dr-occams-r/AntivibrationFanMount/images/Fan4010-ModelView2.png

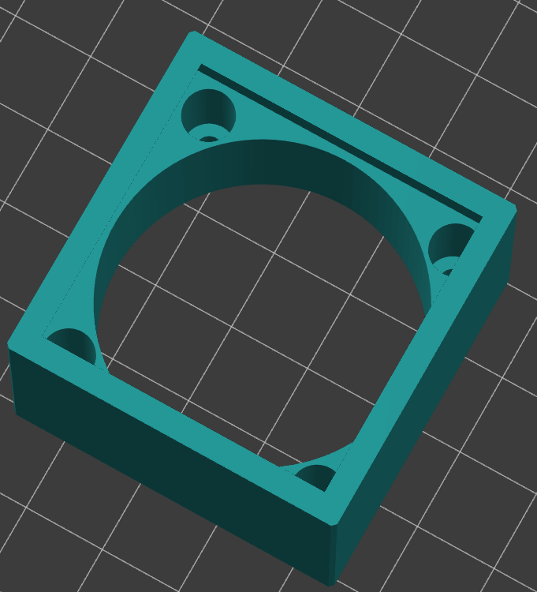
images/Fan4010-ModelView2.png
