dr-occams-r/AntivibrationFanMount/images/IMG_20240214_092702.jpg

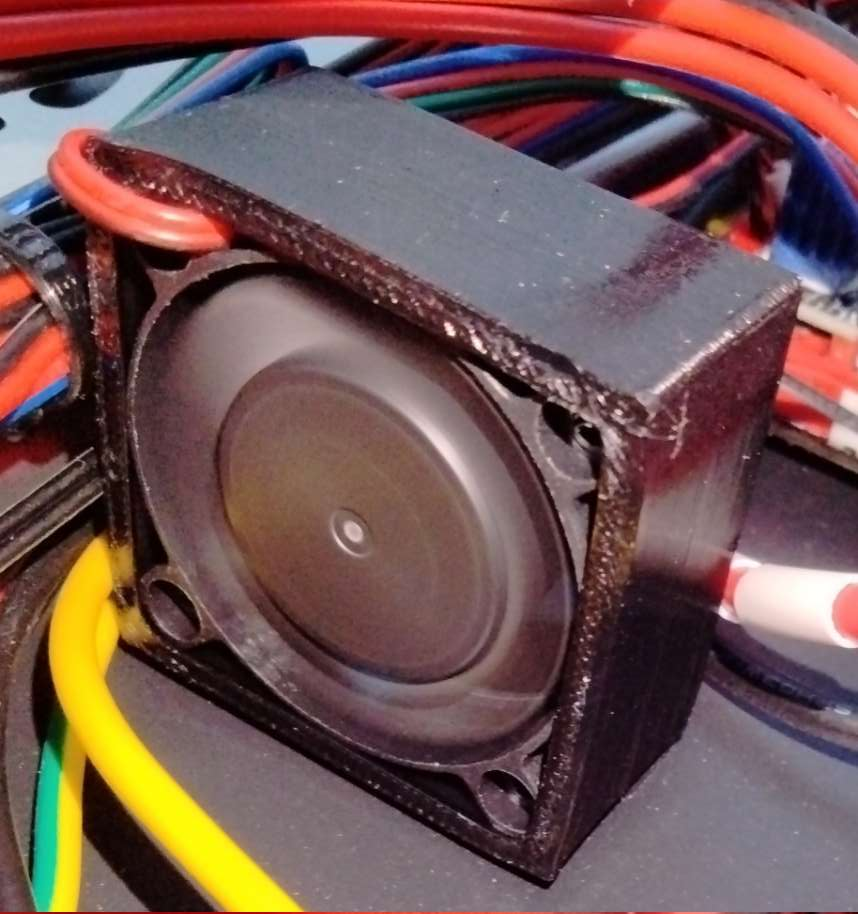
images/IMG_20240214_092702.jpg
