dr-occams-r/AntivibrationFanMount/images/IMG_20240214_092718.jpg

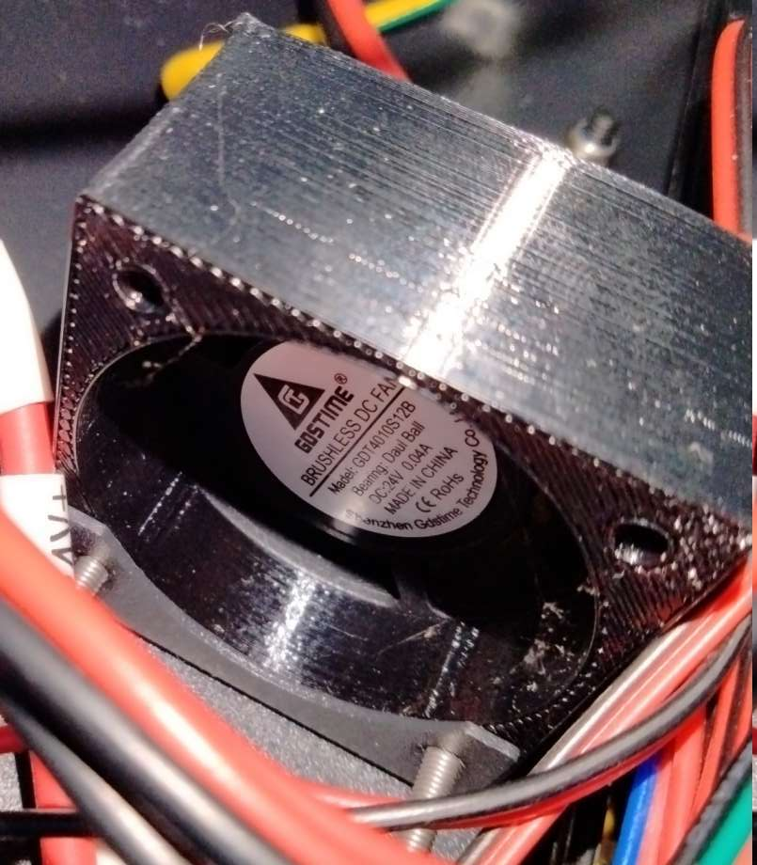
images/IMG_20240214_092718.jpg
